hipe-0/Midi-Arpeggiator/Media/PrintingIn6h.jpg

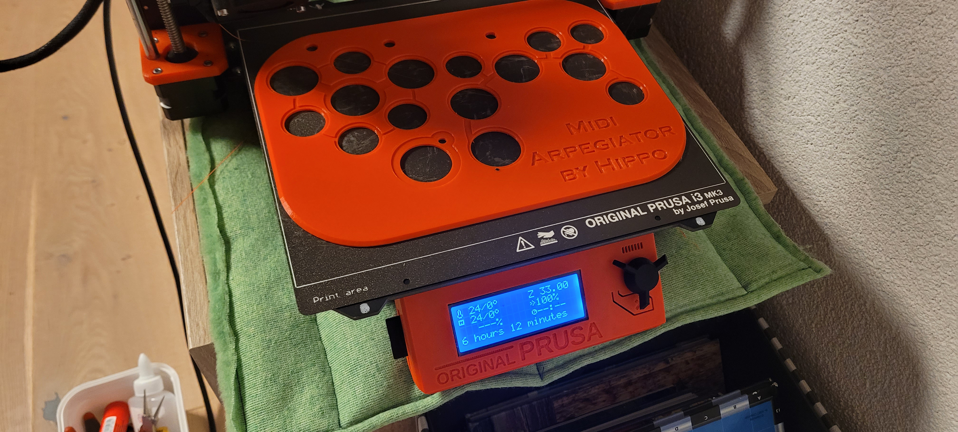
Media/PrintingIn6h.jpg
